pmgducati/Blue-Retro-AIO-Units/STL/Aux Bottom - Sega Genesis-Megadrive Multitap.STL

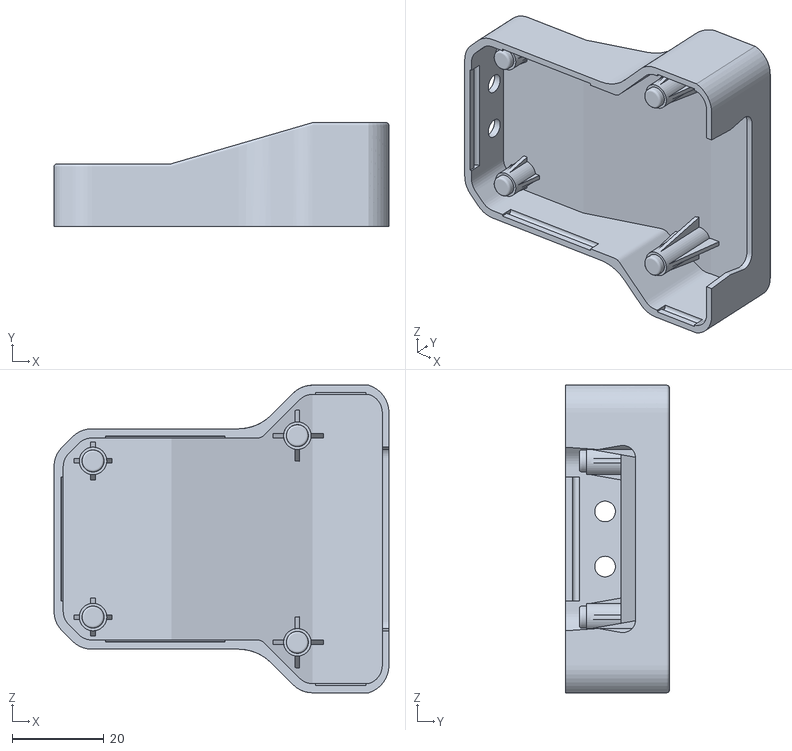
[picture p16: CAD file, 2022-04-20]
STL/Aux Bottom - Sega Genesis-Megadrive Multitap.STL
72.9 x 22.6 x 67.0
