pmgducati/Blue-Retro-AIO-Units/STL/Aux Top - NEC PCEngine.STL

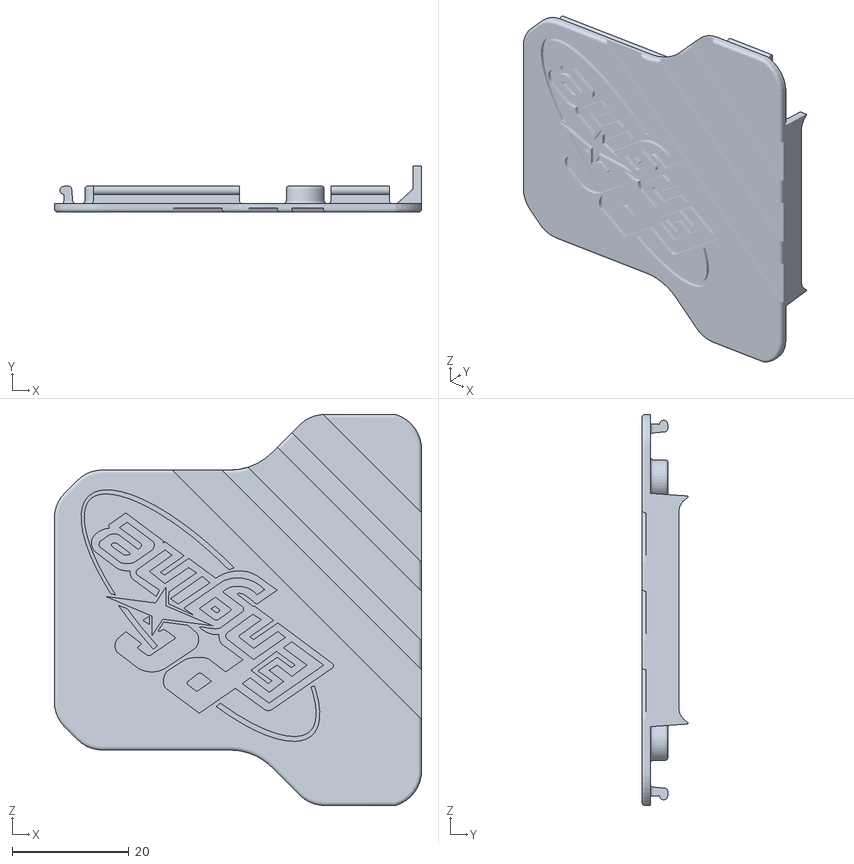
[picture p17: CAD file, 2022-04-15]
STL/Aux Top - NEC PCEngine.STL
63.0 x 7.96 x 67.0
