pmgducati/Blue-Retro-AIO-Units/PCB/SNES.brd

## EAGLE design PCB/SNES.brd (2023-01-09)

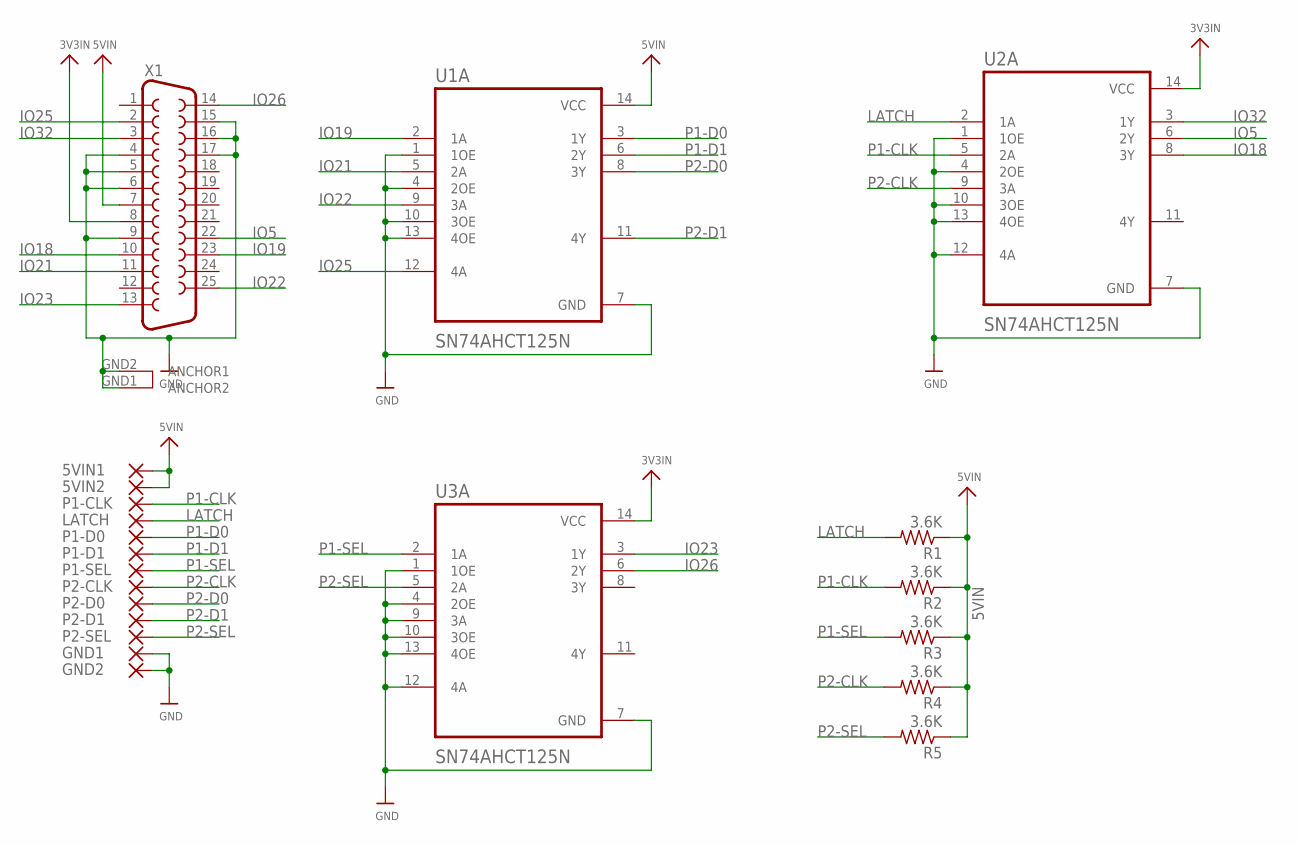
[picture p33: schematic SNES.sch]

Parts:
5VIN1, 5VIN2: SMD5; SMD2,54-5,08
GND1, GND2: SMD5; SMD2,54-5,08
LATCH: SMD5; SMD2,54-5,08
P1-CLK, P1-D0, P1-D1, P1-SEL, P2-CLK, P2-D0, P2-D1, P2-SEL: SMD5; SMD2,54-5,08
R1, R2, R3, R4, R5: 3.6K; R1206
U1A, U2A, U3A: SN74AHCT125N; DIP794W45P254L1969H508Q14
X1: DB25_FEMALEHP; F25HP

Connections:
3V3IN: U2A.14 (VCC), U3A.14 (VCC), X1.8
5VIN: 5VIN1.1, 5VIN2.1, R1.1, R2.1, R3.1, R4.1, R5.1, U1A.14 (VCC), X1.7
GND: GND1.1, GND2.1, U1A.1 (1OE), U1A.4 (2OE), U1A.7 (GND), U1A.10 (3OE), U1A.13 (4OE), U2A.1 (1OE), U2A.4 (2OE), U2A.7 (GND), U2A.10 (3OE), U2A.12 (4A), U2A.13 (4OE), U3A.1 (1OE), U3A.4 (2OE), U3A.7 (GND), U3A.9 (3A), U3A.10 (3OE), U3A.12 (4A), U3A.13 (4OE), X1.4, X1.5, X1.6, X1.9, X1.15, X1.16, X1.17, X1.GND1 (ANCHOR2), X1.GND2 (ANCHOR1)
IO5: U2A.6 (2Y), X1.22
IO18: U2A.8 (3Y), X1.10
IO19: U1A.2 (1A), X1.23
IO21: U1A.5 (2A), X1.11
IO22: U1A.9 (3A), X1.25
IO23: U3A.3 (1Y), X1.13
IO25: U1A.12 (4A), X1.2
IO26: U3A.6 (2Y), X1.14
IO32: U2A.3 (1Y), X1.3
LATCH: LATCH.1, R1.2, U2A.2 (1A)
P1-CLK: P1-CLK.1, R2.2, U2A.5 (2A)
P1-D0: P1-D0.1, U1A.3 (1Y)
P1-D1: P1-D1.1, U1A.6 (2Y)
P1-SEL: P1-SEL.1, R3.2, U3A.2 (1A)
P2-CLK: P2-CLK.1, R4.2, U2A.9 (3A)
P2-D0: P2-D0.1, U1A.8 (3Y)
P2-D1: P2-D1.1, U1A.11 (4Y)
P2-SEL: P2-SEL.1, R5.2, U3A.5 (2A)

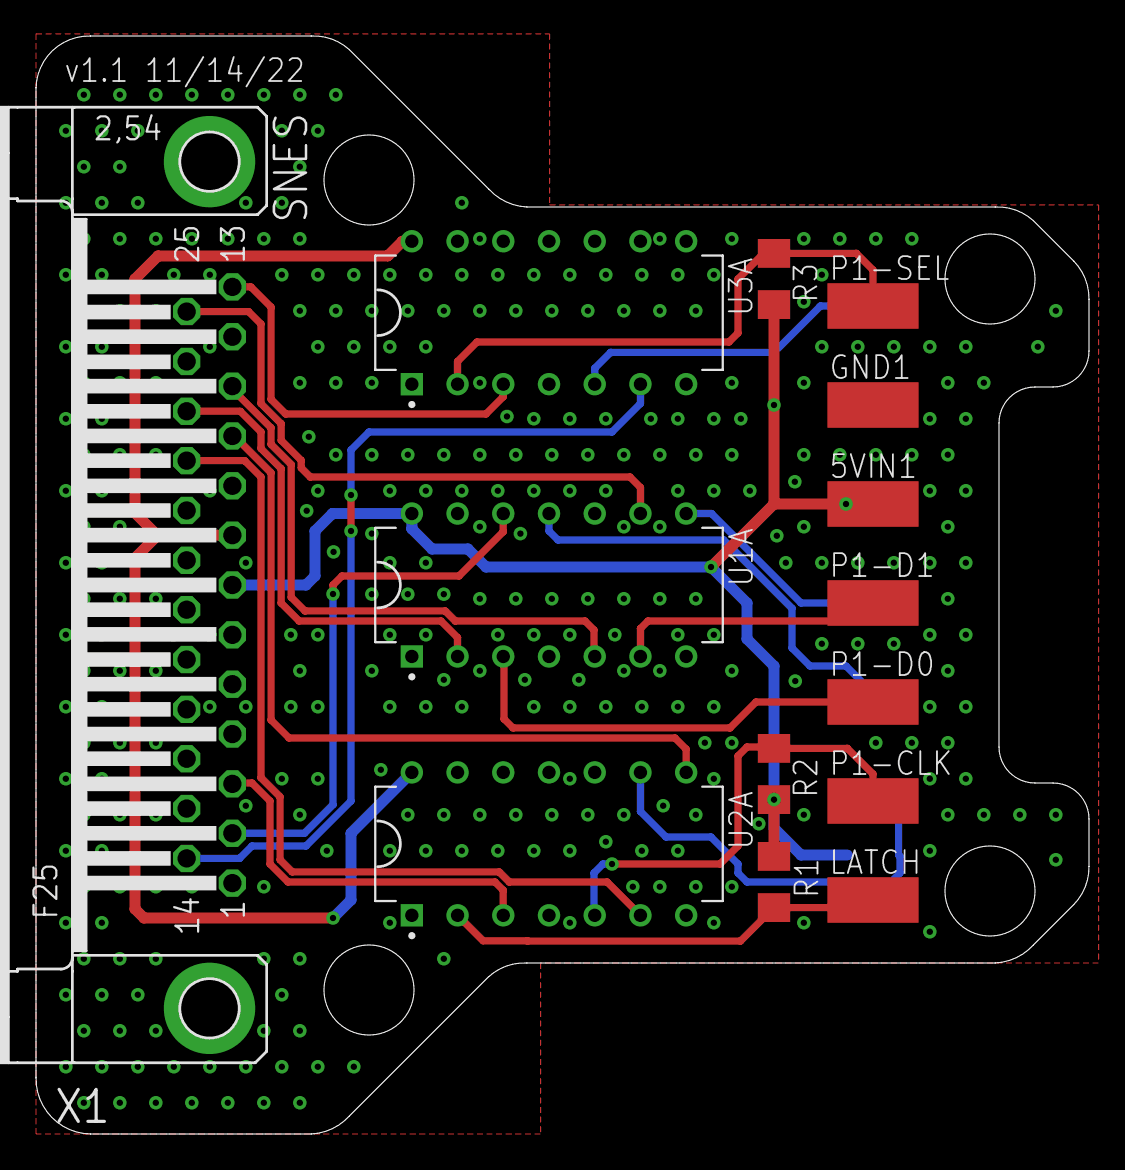
[picture p34: board SNES.brd from above]

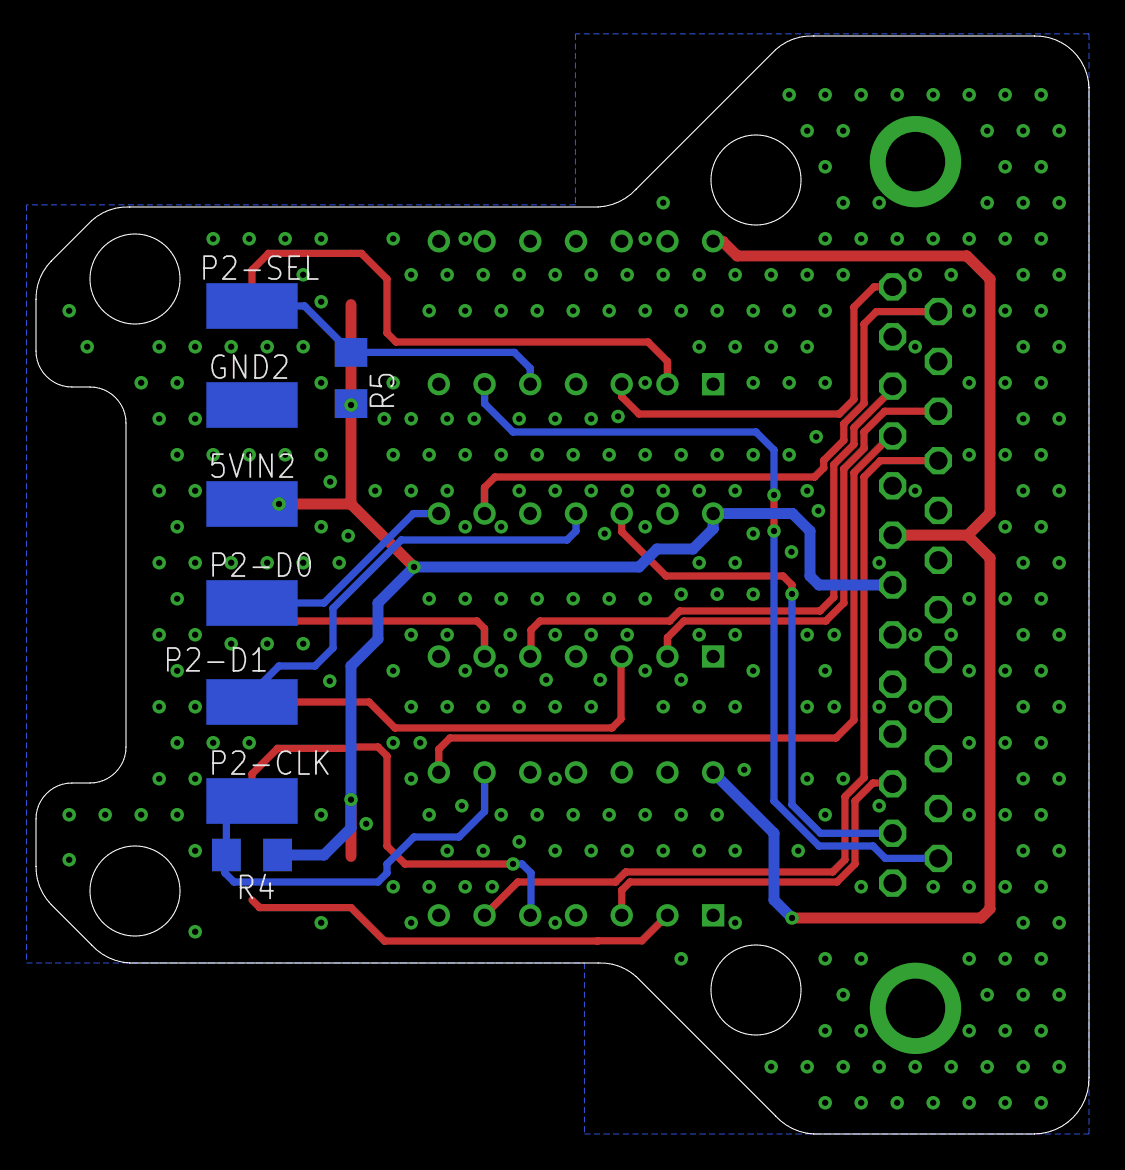
[picture p35: board SNES.brd from below]

Board: 2 copper layers, 58.5 x 61.0 mm, 22 parts (8 on the bottom side), 21 nets.
