pmgducati/Blue-Retro-AIO-Units/PCB/CDi.brd

## EAGLE design PCB/CDi.brd (2023-01-09)

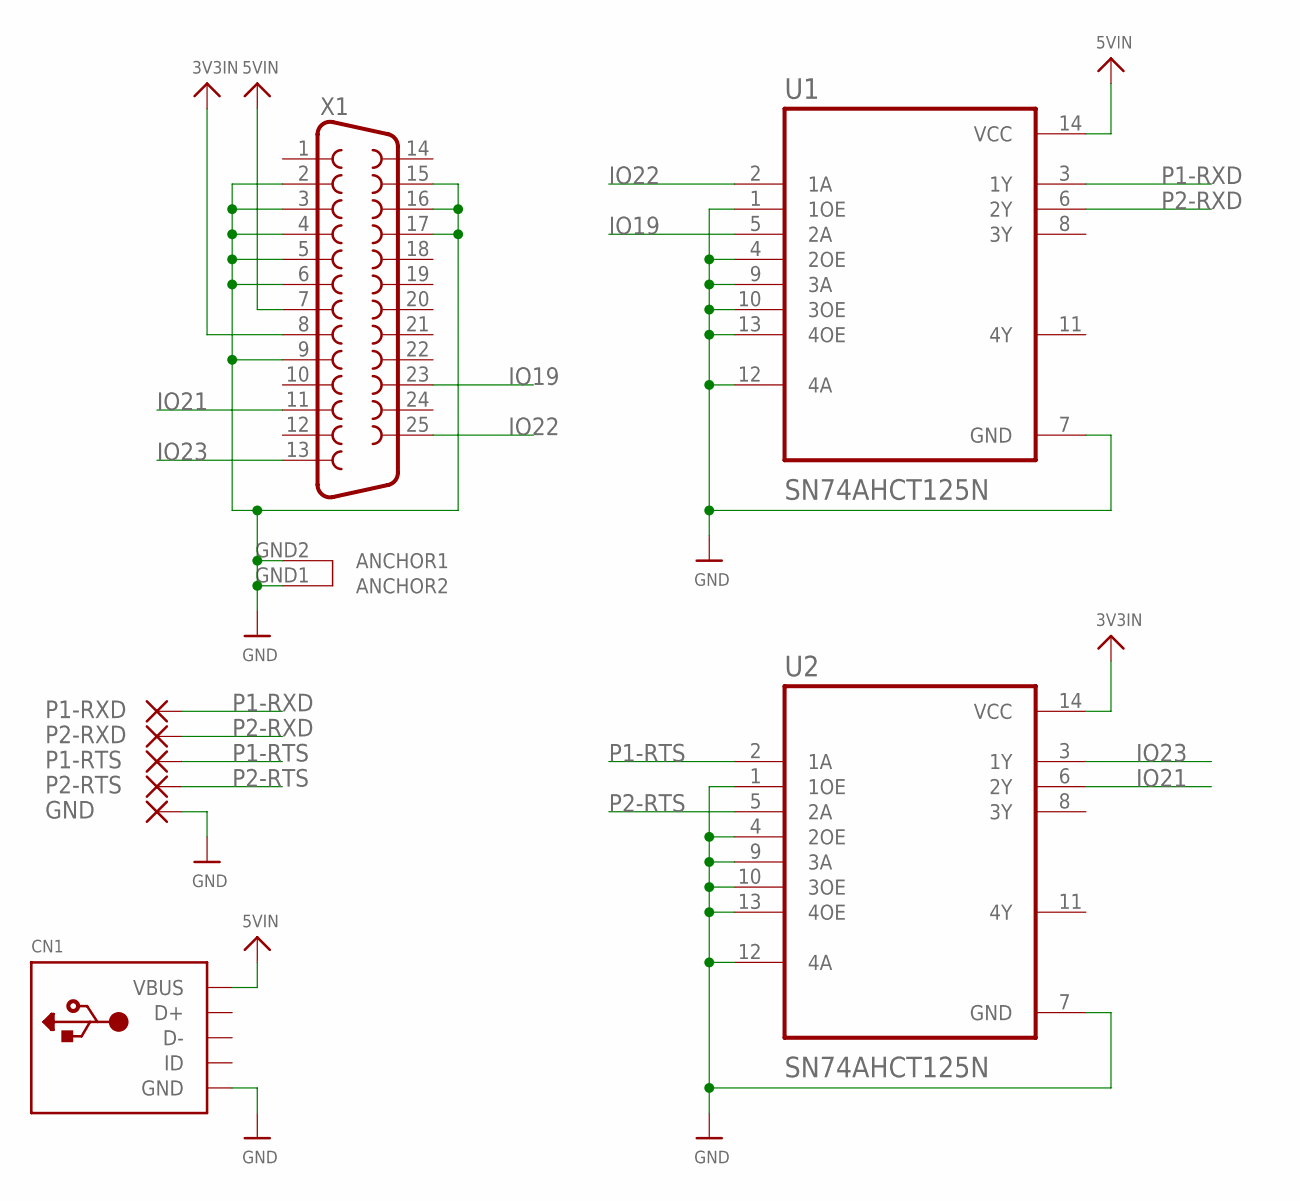
[picture p36: schematic CDi.sch]

Parts:
CN1: USBTHM; USB-MINIB-THM
GND: SMD5; SMD2,54-5,08
P1-RTS, P1-RXD, P2-RTS, P2-RXD: SMD5; SMD2,54-5,08
U1, U2: SN74AHCT125N; DIP794W45P254L1969H508Q14
X1: DB25_FEMALEHP; F25HP

Connections:
3V3IN: U2.14 (VCC), X1.8
5VIN: CN1.VBUS, U1.14 (VCC), X1.7
GND: CN1.GND, GND.1, U1.1 (1OE), U1.4 (2OE), U1.7 (GND), U1.9 (3A), U1.10 (3OE), U1.12 (4A), U1.13 (4OE), U2.1 (1OE), U2.4 (2OE), U2.7 (GND), U2.9 (3A), U2.10 (3OE), U2.12 (4A), U2.13 (4OE), X1.2, X1.3, X1.4, X1.5, X1.6, X1.9, X1.15, X1.16, X1.17, X1.GND1 (ANCHOR2), X1.GND2 (ANCHOR1)
IO19: U1.5 (2A), X1.23
IO21: U2.6 (2Y), X1.11
IO22: U1.2 (1A), X1.25
IO23: U2.3 (1Y), X1.13
P1-RTS: P1-RTS.1, U2.2 (1A)
P1-RXD: P1-RXD.1, U1.3 (1Y)
P2-RTS: P2-RTS.1, U2.5 (2A)
P2-RXD: P2-RXD.1, U1.6 (2Y)

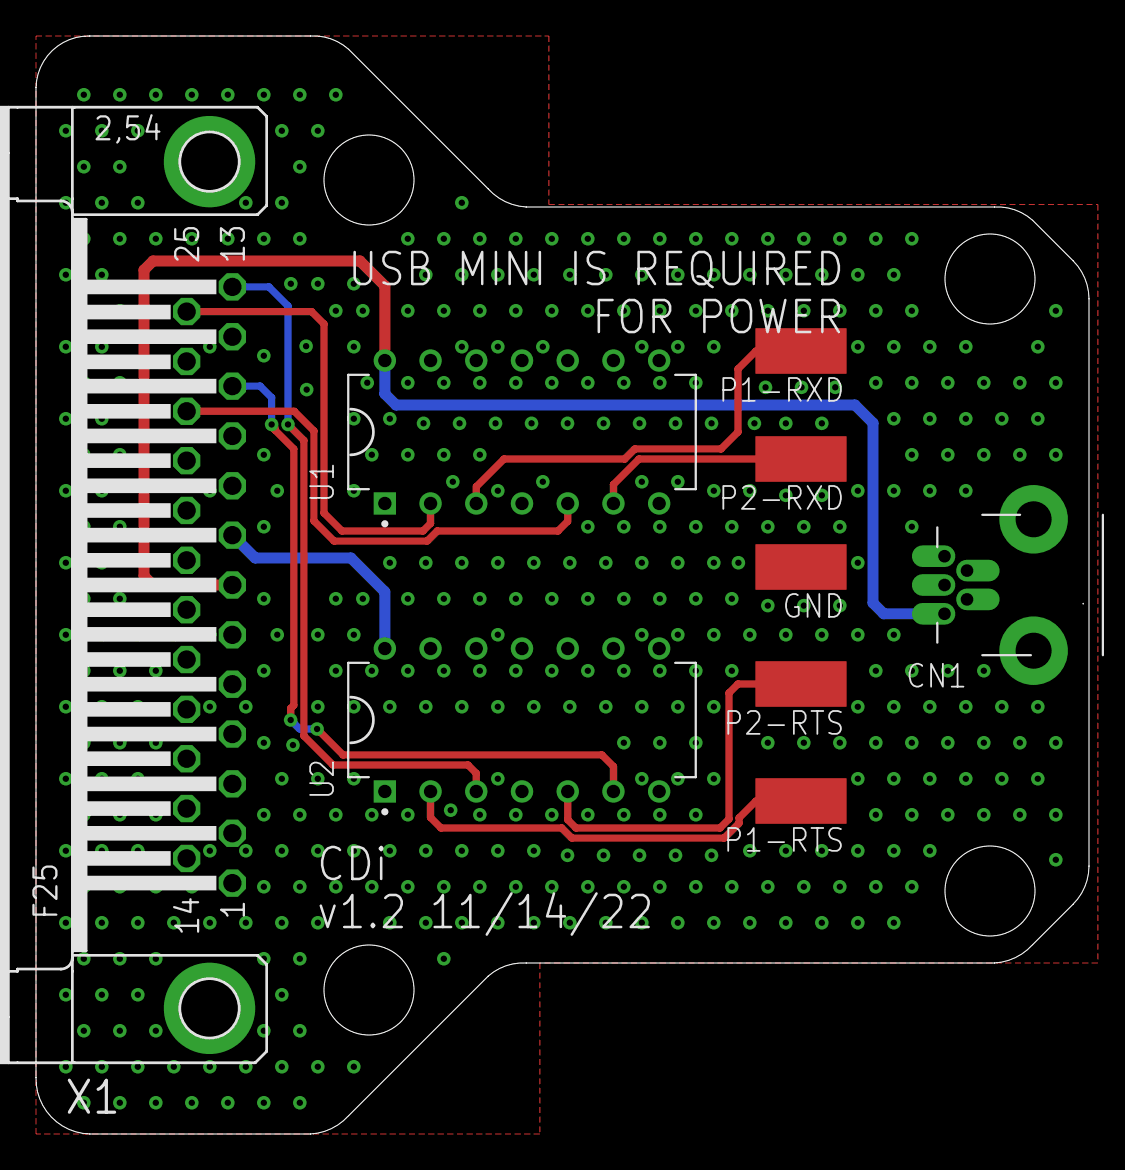
[picture p37: board CDi.brd from above]

Board: 2 copper layers, 58.5 x 61.0 mm, 9 parts (0 on the bottom side), 11 nets.
