pmgducati/Blue-Retro-AIO-Units/PCB/Wiiext-NES Mini-SNES Mini.brd

## EAGLE design PCB/Wiiext-NES Mini-SNES Mini.brd (2022-12-28)

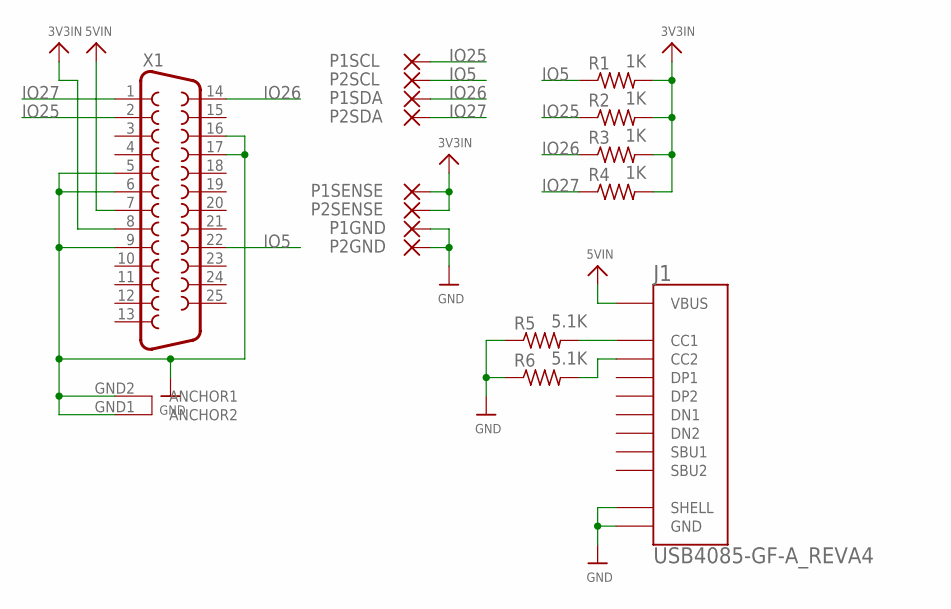
[picture p38: schematic Wiiext-NES Mini-SNES Mini.sch]

Parts:
J1: USB4085-GF-A_REVA4; GCT_USB4085-GF-A_REVA4
P1GND, P1SCL, P1SDA, P1SENSE, P2GND, P2SCL, P2SDA, P2SENSE: SMD5; SMD2,54-5,08
R1, R2, R3, R4: 1K; R1206
R5, R6: 5.1K; R1206
X1: DB25_FEMALEHP; F25HP

Connections:
3V3IN: P1SENSE.1, P2SENSE.1, R1.2, R2.2, R3.2, R4.2, X1.8
5VIN: J1.A4 (VBUS), J1.A9 (VBUS), J1.B4 (VBUS), J1.B9 (VBUS), X1.7
GND: J1.A1 (GND), J1.A12 (GND), J1.B1 (GND), J1.B12 (GND), J1.S1 (SHELL), J1.S2 (SHELL), J1.S3 (SHELL), J1.S4 (SHELL), P1GND.1, P2GND.1, R5.1, R6.1, X1.5, X1.6, X1.9, X1.16, X1.17, X1.GND1 (ANCHOR2), X1.GND2 (ANCHOR1)
IO5: P2SCL.1, R1.1, X1.22
IO25: P1SCL.1, R2.1, X1.2
IO26: P1SDA.1, R3.1, X1.14
IO27: P2SDA.1, R4.1, X1.1
PD1: J1.B5 (CC2), R6.2
PD2: J1.A5 (CC1), R5.2

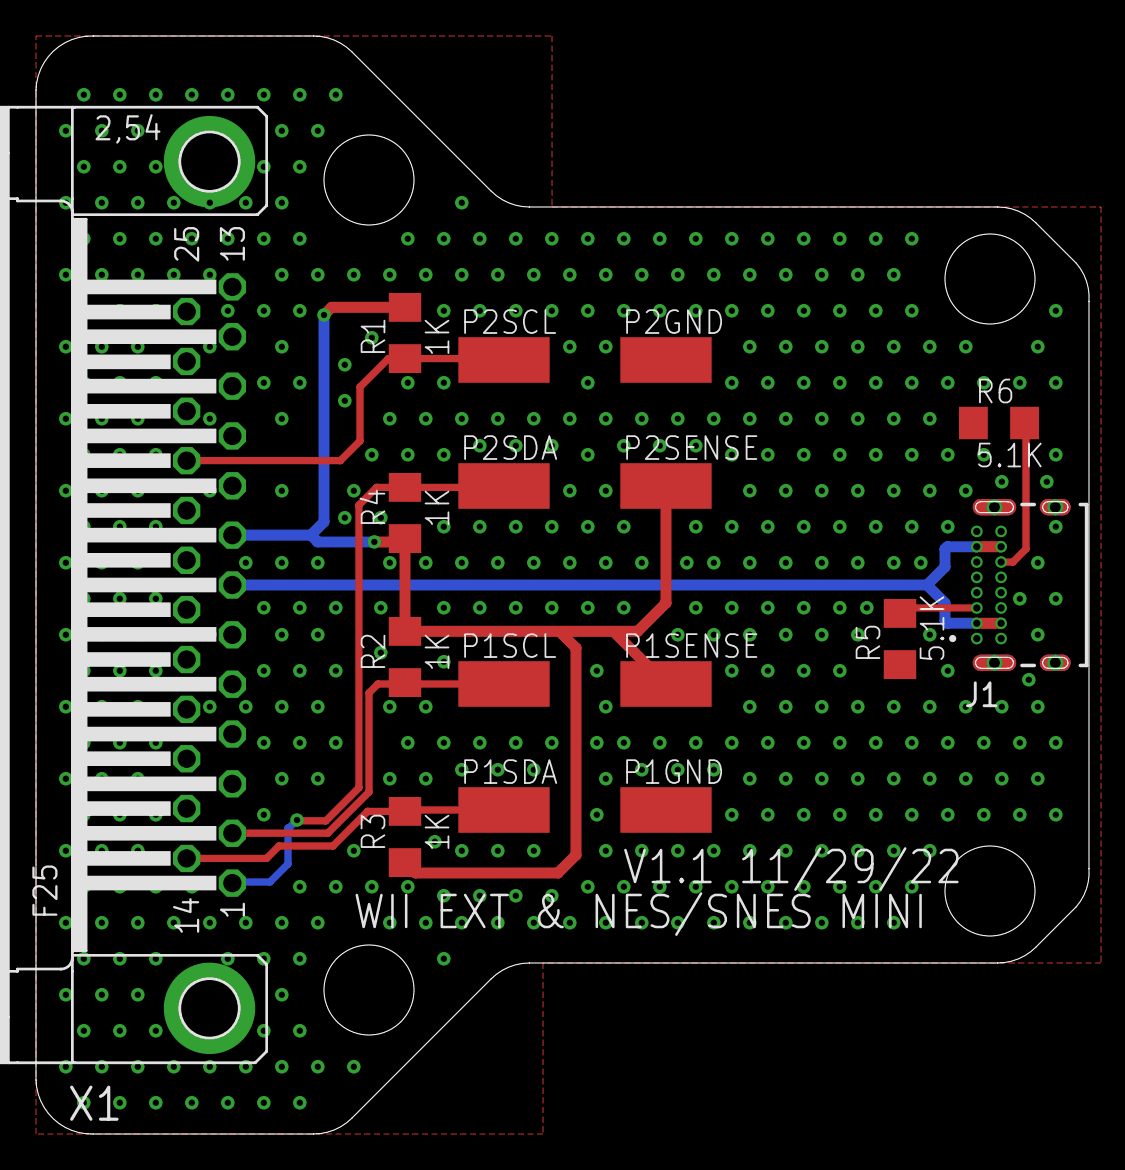
[picture p39: board Wiiext-NES Mini-SNES Mini.brd from above]

Board: 2 copper layers, 58.5 x 61.0 mm, 16 parts (0 on the bottom side), 9 nets.
