pmgducati/Blue-Retro-AIO-Units/PCB/Main.brd

## EAGLE design PCB/Main.brd (2022-11-14)

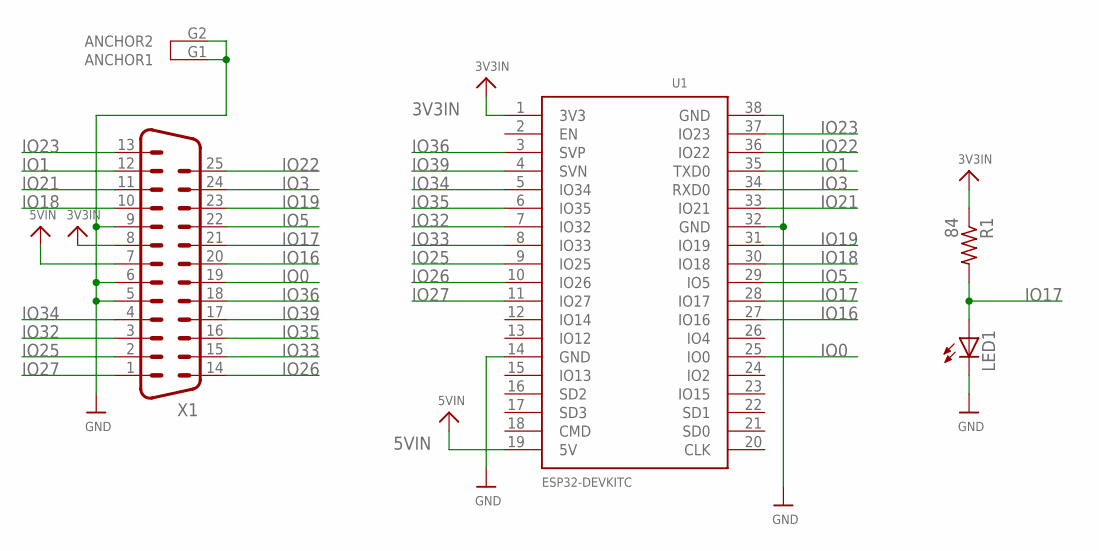
[picture p40: schematic Main.sch]

Parts:
LED1: LEDCHIPLED_1206; CHIPLED_1206
R1: 84; R1206
U1: ESP32DEVKITC; ESP32-DEVKITC
X1: DB25_MALEHP; M25HP

Connections:
3V3IN: R1.1, U1.1 (3V3), X1.8
5VIN: U1.19 (5V), X1.7
GND: LED1.C, U1.14 (GND), U1.32 (GND), U1.38 (GND), X1.5, X1.6, X1.9, X1.G1 (ANCHOR1), X1.G2 (ANCHOR2)
IO0: U1.25 (IO0), X1.19
IO1: U1.35 (TXD0), X1.12
IO3: U1.34 (RXD0), X1.24
IO5: U1.29 (IO5), X1.22
IO16: U1.27 (IO16), X1.20
IO17: LED1.A, R1.2, U1.28 (IO17), X1.21
IO18: U1.30 (IO18), X1.10
IO19: U1.31 (IO19), X1.23
IO21: U1.33 (IO21), X1.11
IO22: U1.36 (IO22), X1.25
IO23: U1.37 (IO23), X1.13
IO25: U1.9 (IO25), X1.2
IO26: U1.10 (IO26), X1.14
IO27: U1.11 (IO27), X1.1
IO32: U1.7 (IO32), X1.3
IO33: U1.8 (IO33), X1.15
IO34: U1.5 (IO34), X1.4
IO35: U1.6 (IO35), X1.16
IO36: U1.3 (SVP), X1.18
IO39: U1.4 (SVN), X1.17

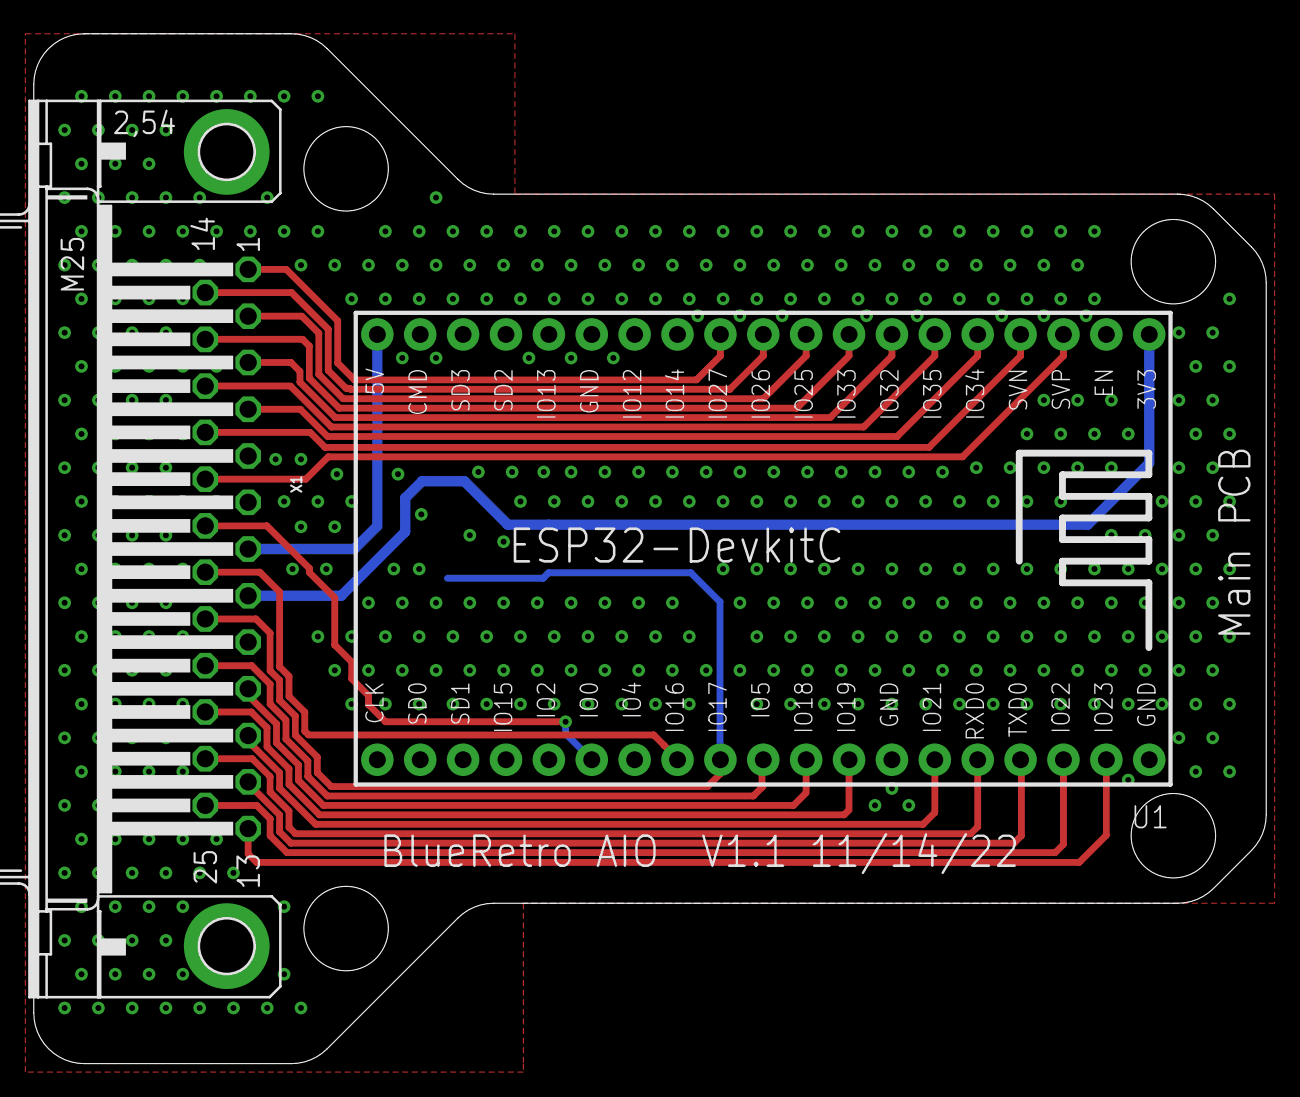
[picture p41: board Main.brd from above]

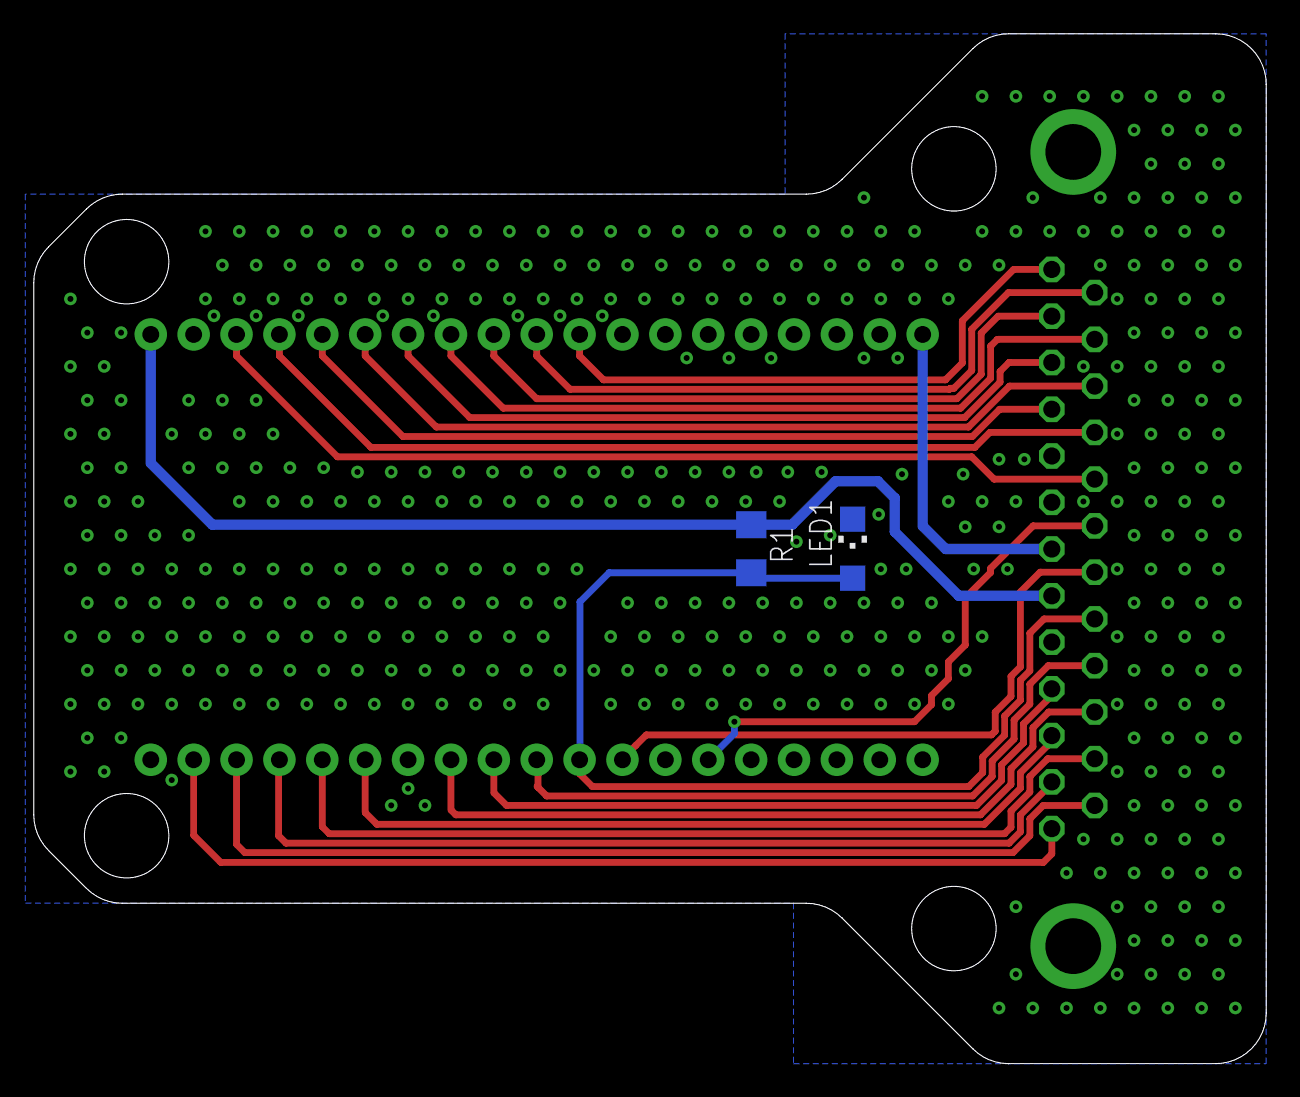
[picture p42: board Main.brd from below]

Board: 2 copper layers, 73.0 x 61.0 mm, 4 parts (2 on the bottom side), 23 nets.
