pmgducati/Blue-Retro-AIO-Units/PCB/Gamecube.brd

## EAGLE design PCB/Gamecube.brd (2022-11-14)

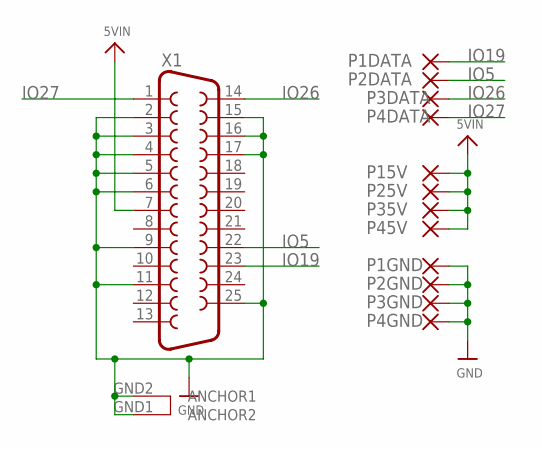
[picture p43: schematic Gamecube.sch]

Parts:
P1DATA, P1GND, P2DATA, P2GND, P3DATA, P3GND, P4DATA, P4GND, P15V, P25V, P35V, P45V: SMD5; SMD2,54-5,08
X1: DB25_FEMALEHP; F25HP

Connections:
5VIN: P15V.1, P25V.1, P35V.1, P45V.1, X1.7
GND: P1GND.1, P2GND.1, P3GND.1, P4GND.1, X1.2, X1.3, X1.4, X1.5, X1.6, X1.9, X1.11, X1.15, X1.16, X1.17, X1.25, X1.GND1 (ANCHOR2), X1.GND2 (ANCHOR1)
IO5: P2DATA.1, X1.22
IO19: P1DATA.1, X1.23
IO26: P3DATA.1, X1.14
IO27: P4DATA.1, X1.1

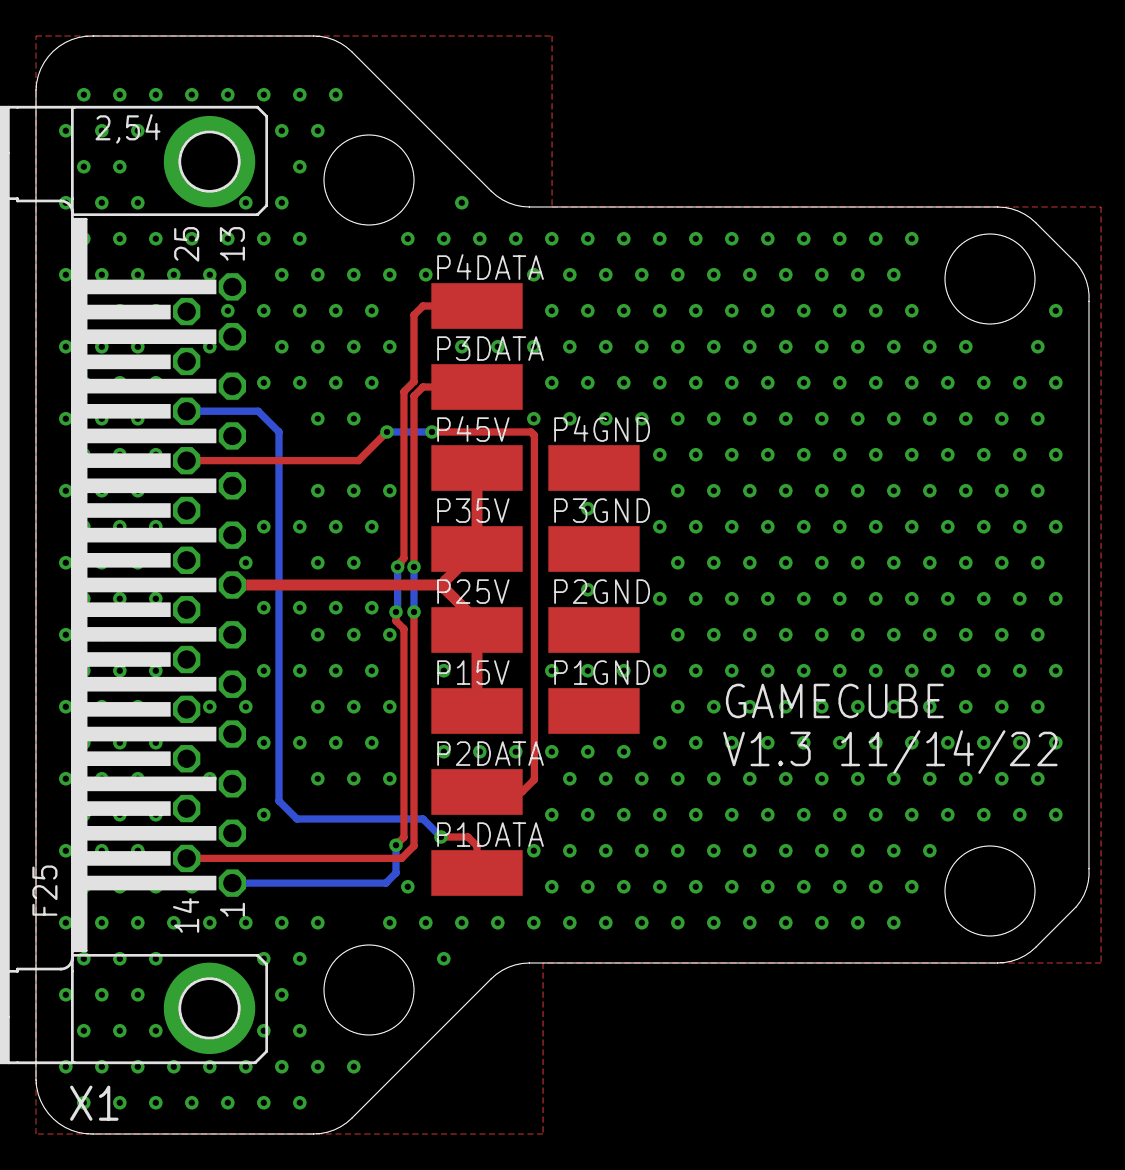
[picture p44: board Gamecube.brd from above]

Board: 2 copper layers, 58.5 x 61.0 mm, 13 parts (0 on the bottom side), 6 nets.
