pmgducati/Blue-Retro-AIO-Units/PCB/PSX-PS2.brd

## EAGLE design PCB/PSX-PS2.brd (2022-11-14)

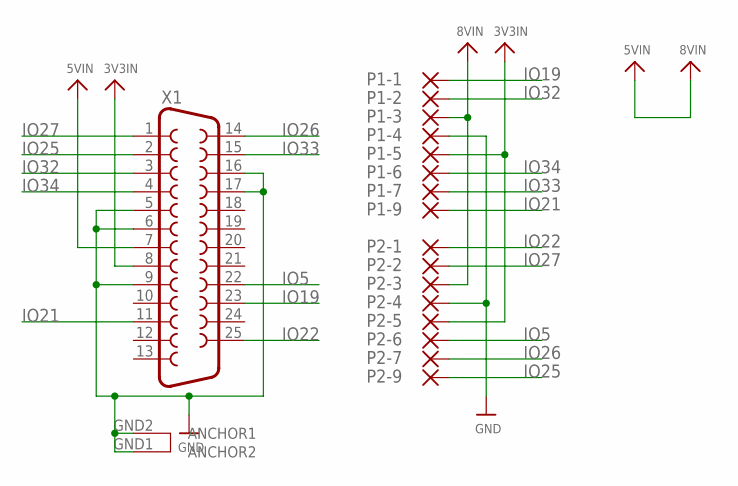
[picture p45: schematic PSX-PS2.sch]

Parts:
P1-1, P1-2, P1-3, P1-4, P1-5, P1-6, P1-7, P1-9, P2-1, P2-2, P2-3, P2-4, P2-5, P2-6, P2-7, P2-9: SMD5; SMD2,54-5,08
X1: DB25_FEMALEHP; F25HP

Connections:
3V3IN: P1-5.1, P2-5.1, X1.8
GND: P1-4.1, P2-4.1, X1.5, X1.6, X1.9, X1.16, X1.17, X1.GND1 (ANCHOR2), X1.GND2 (ANCHOR1)
IO5: P2-6.1, X1.22
IO19: P1-1.1, X1.23
IO21: P1-9.1, X1.11
IO22: P2-1.1, X1.25
IO25: P2-9.1, X1.2
IO26: P2-7.1, X1.14
IO27: P2-2.1, X1.1
IO32: P1-2.1, X1.3
IO33: P1-7.1, X1.15
IO34: P1-6.1, X1.4
VIN: P1-3.1, P2-3.1, X1.7

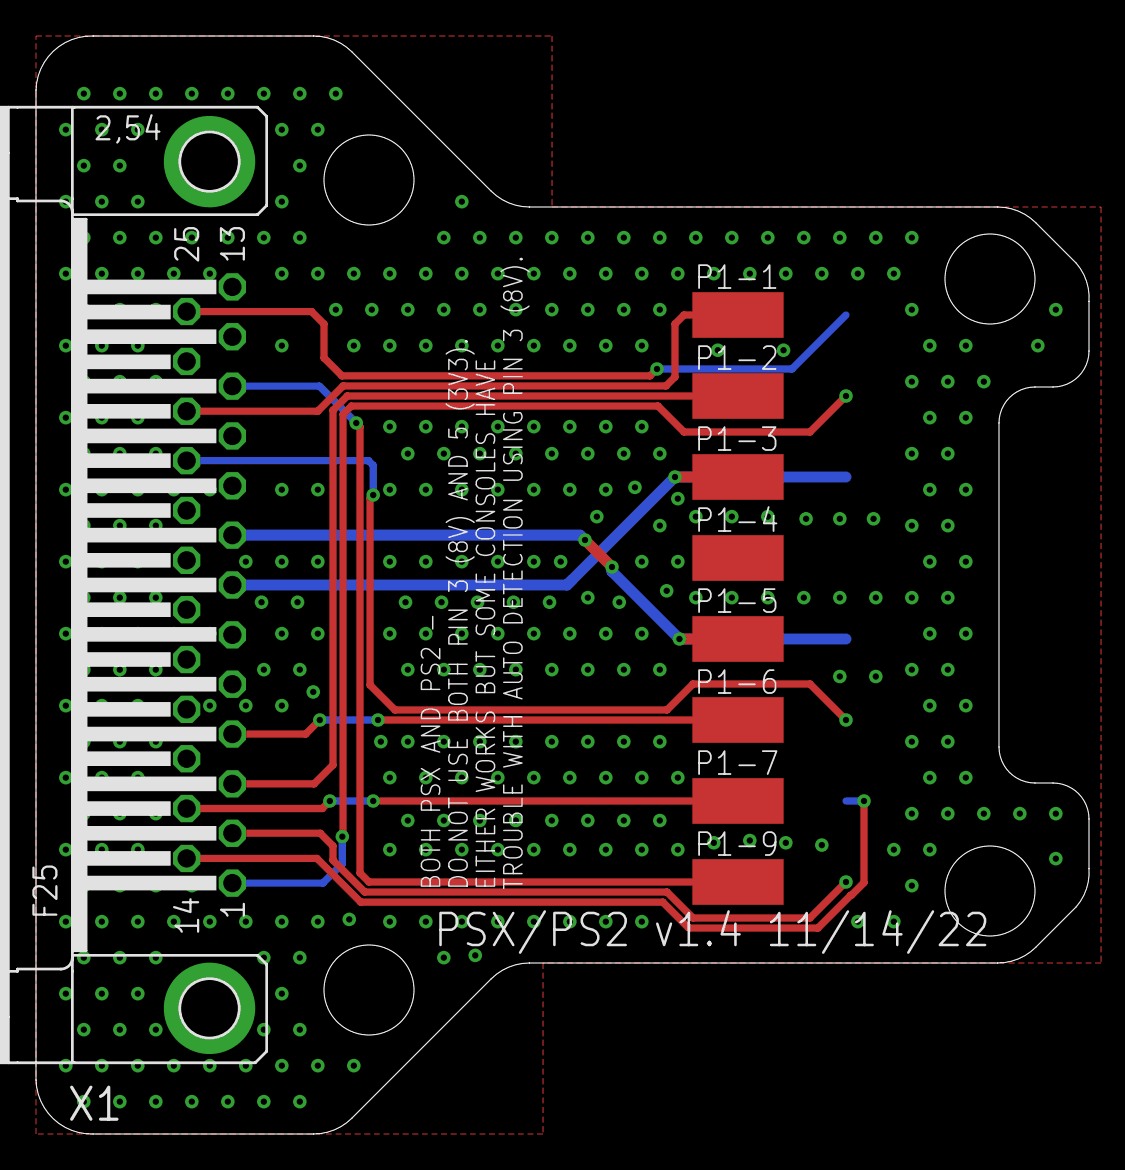
[picture p46: board PSX-PS2.brd from above]

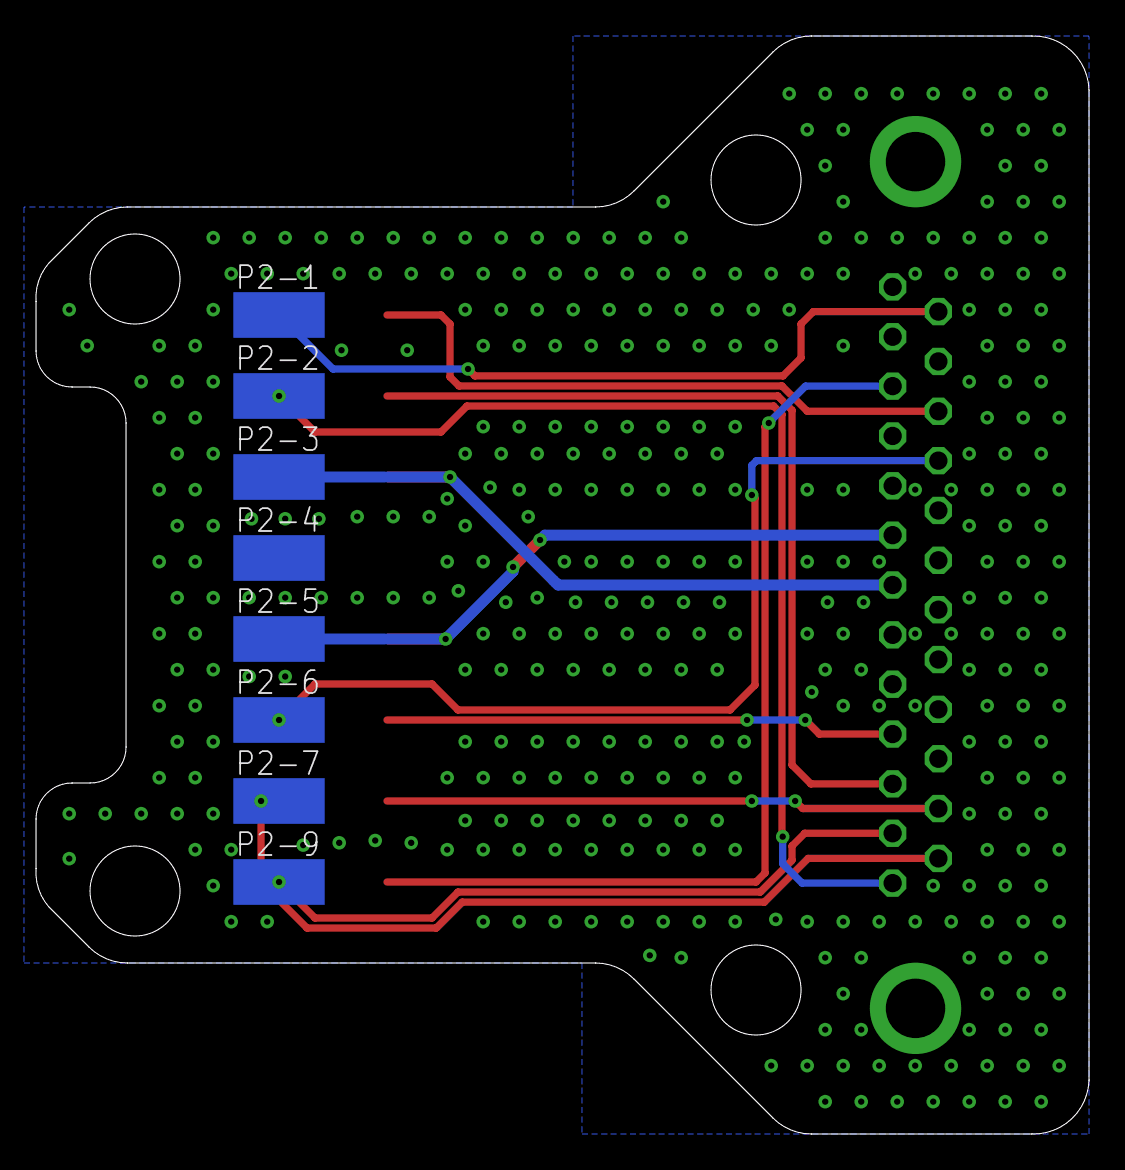
[picture p47: board PSX-PS2.brd from below]

Board: 2 copper layers, 58.5 x 61.0 mm, 17 parts (8 on the bottom side), 13 nets.
